KonkArLab/KOSMOS/docs/doc/kosmos/pictures/deployment/filtre_lens.jpg

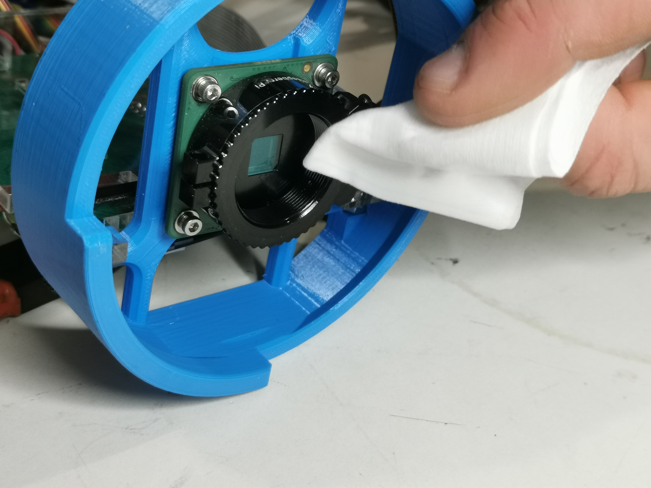
docs/doc/kosmos/pictures/deployment/filtre_lens.jpg
