KonkArLab/KOSMOS/docs/doc/kosmos/pictures/deployment/mire.jpg

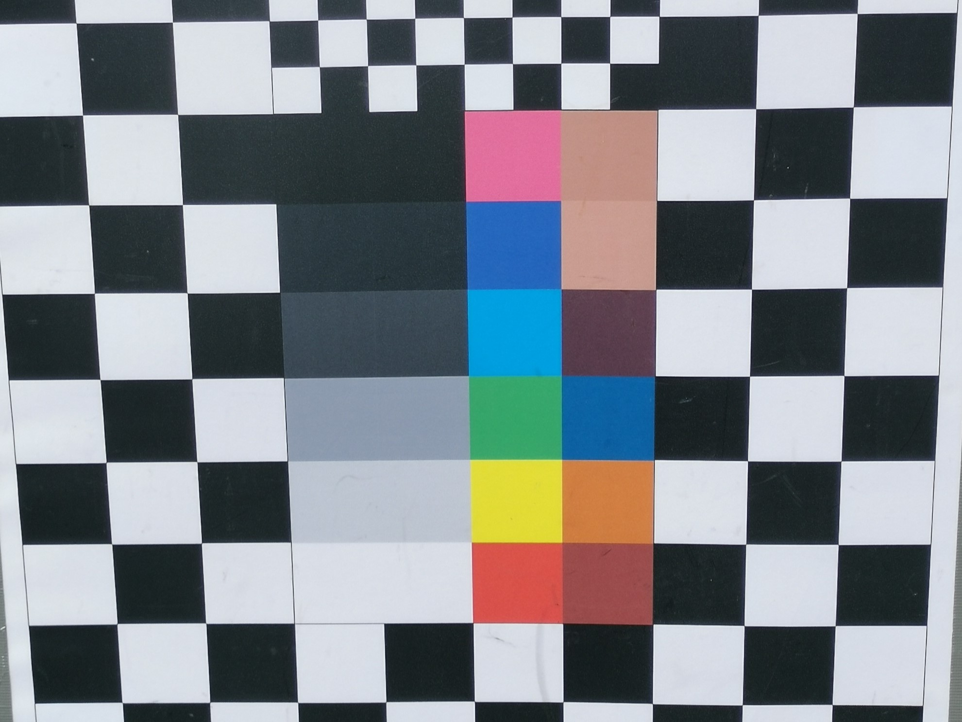
docs/doc/kosmos/pictures/deployment/mire.jpg
