KonkArLab/KOSMOS/docs/doc/kosmos/pictures/deployment/objectif.jpg

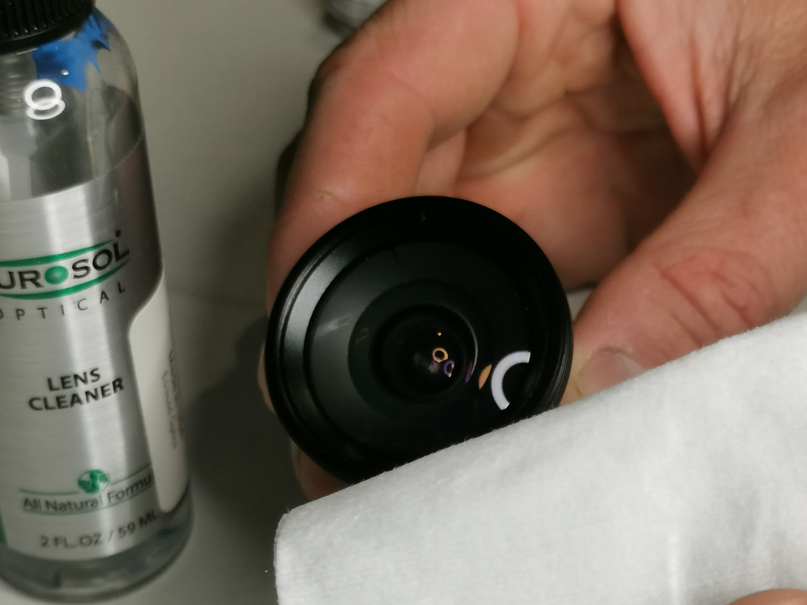
docs/doc/kosmos/pictures/deployment/objectif.jpg
