KonkArLab/KOSMOS/docs/doc/kosmos/pictures/deployment/vis_reglage.jpg

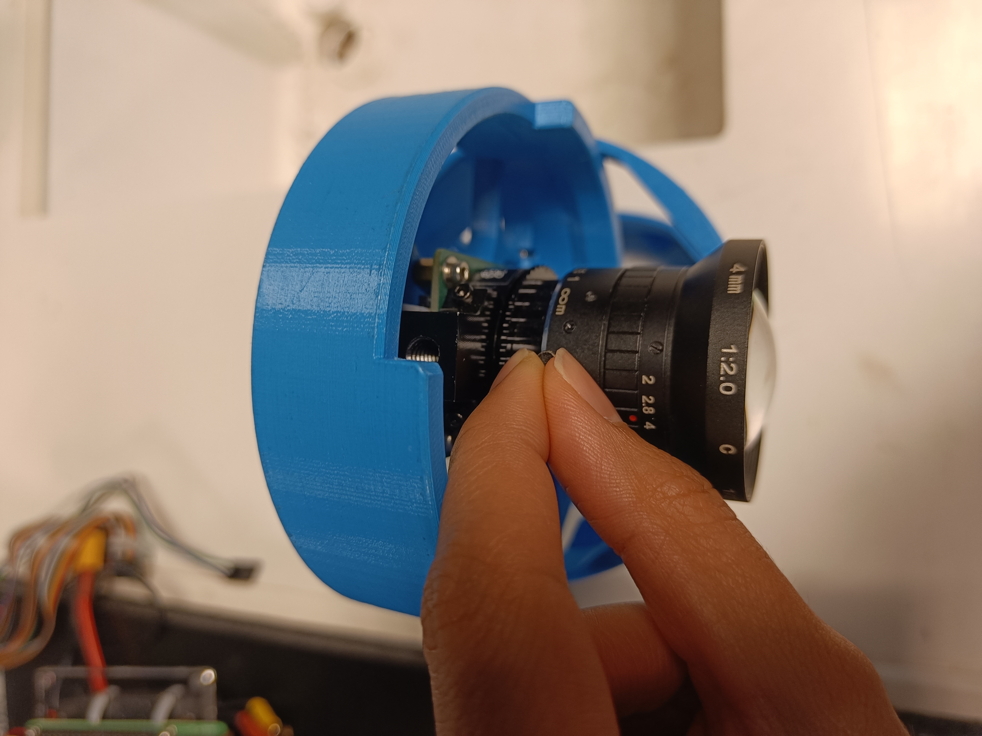
docs/doc/kosmos/pictures/deployment/vis_reglage.jpg
