KonkArLab/KOSMOS/docs/doc/micro_kosmos/pictures/equipments/boitier/clavier_.png

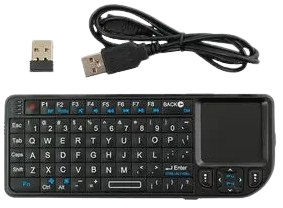
docs/doc/micro_kosmos/pictures/equipments/boitier/clavier_.png
