KonkArLab/KOSMOS/docs/doc/micro_kosmos/pictures/equipments/cable/8pin_cable.png

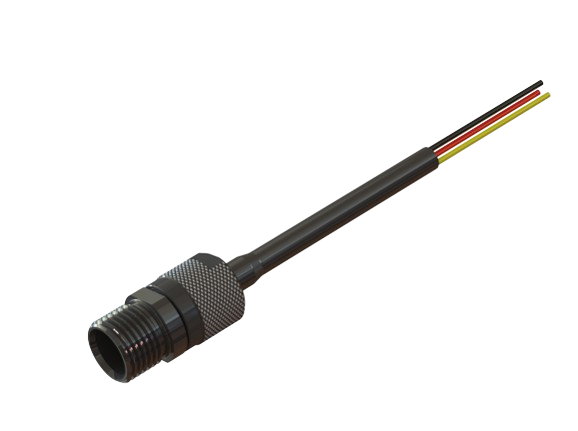
docs/doc/micro_kosmos/pictures/equipments/cable/8pin_cable.png
