KonkArLab/KOSMOS/docs/doc/micro_kosmos/pictures/equipments/caisson_video/ventm10.PNG

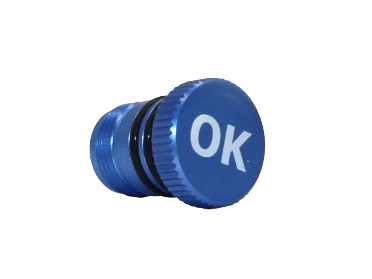
docs/doc/micro_kosmos/pictures/equipments/caisson_video/ventm10.PNG
