KonkArLab/KOSMOS/docs/hardware/kosmos/electronics/electronic.png

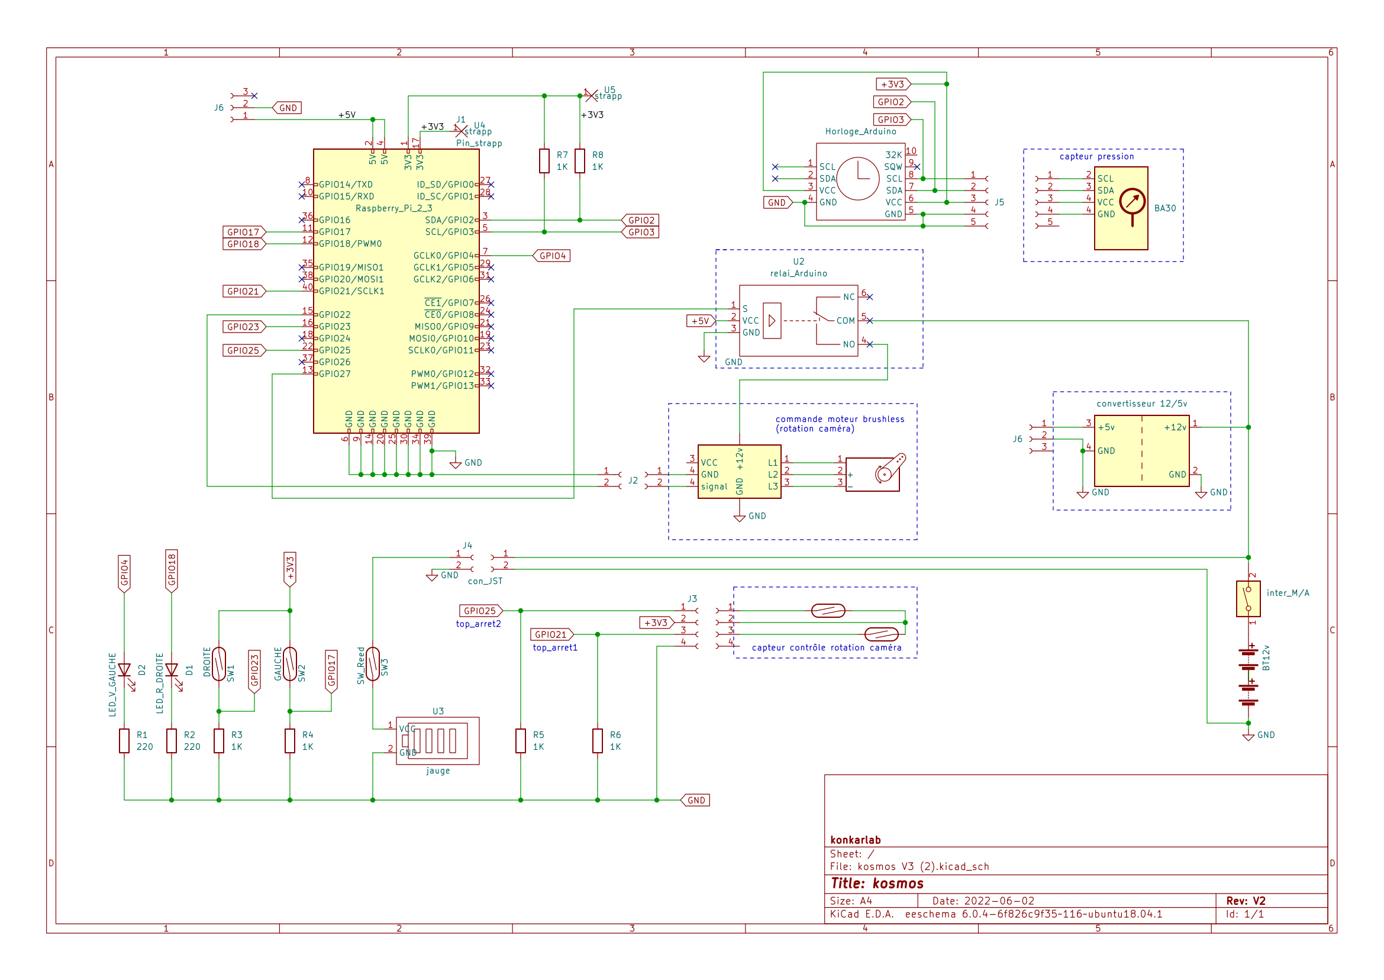
docs/hardware/kosmos/electronics/electronic.png
