KonkArLab/KOSMOS/docs/doc/kosmos/pictures/productions_of_parts/IMG_20230210_140606.jpg

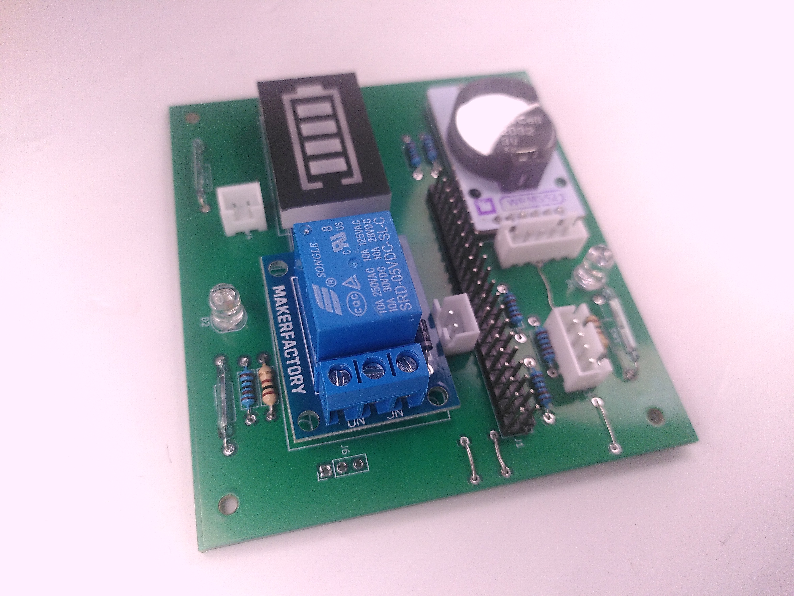
docs/doc/kosmos/pictures/productions_of_parts/IMG_20230210_140606.jpg
