KonkArLab/KOSMOS/docs/doc/kosmos/pictures/productions_of_parts/POP1-1.PNG

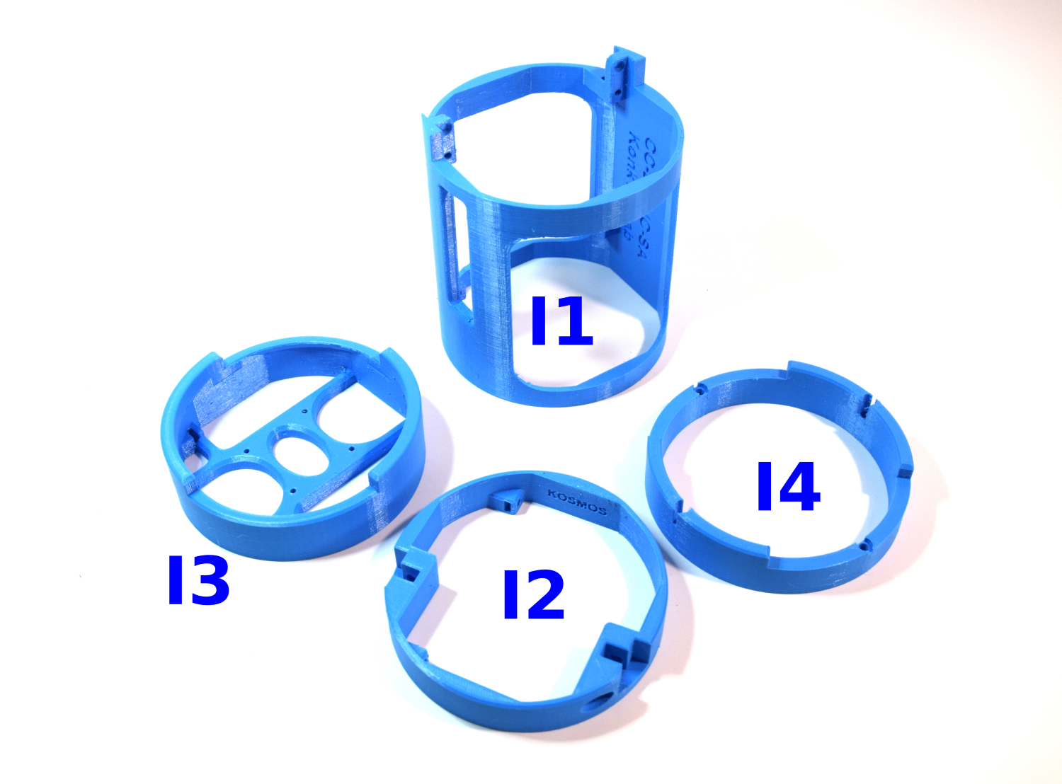
docs/doc/kosmos/pictures/productions_of_parts/POP1-1.PNG
