KonkArLab/KOSMOS/docs/doc/kosmos/pictures/productions_of_parts/POP1-2.PNG

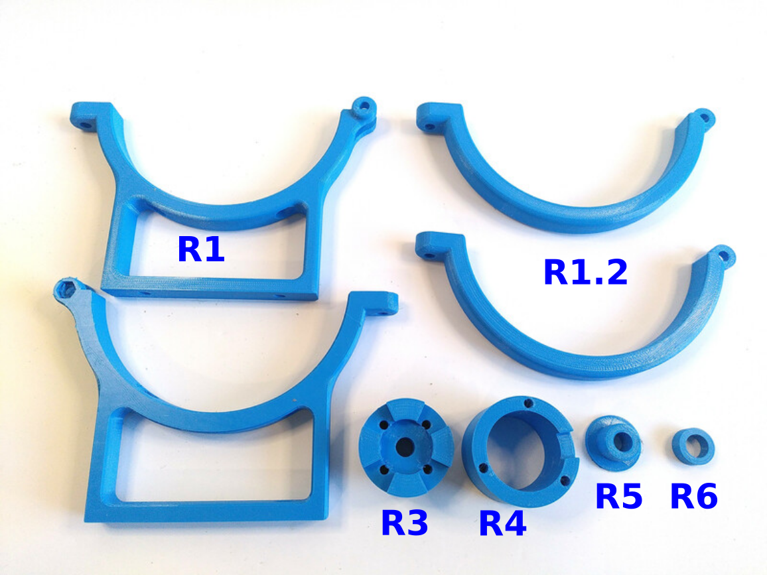
docs/doc/kosmos/pictures/productions_of_parts/POP1-2.PNG
