KonkArLab/KOSMOS/docs/hardware/kosmos/3Dprint_files/R3_KOSMOS_V3-0.stl

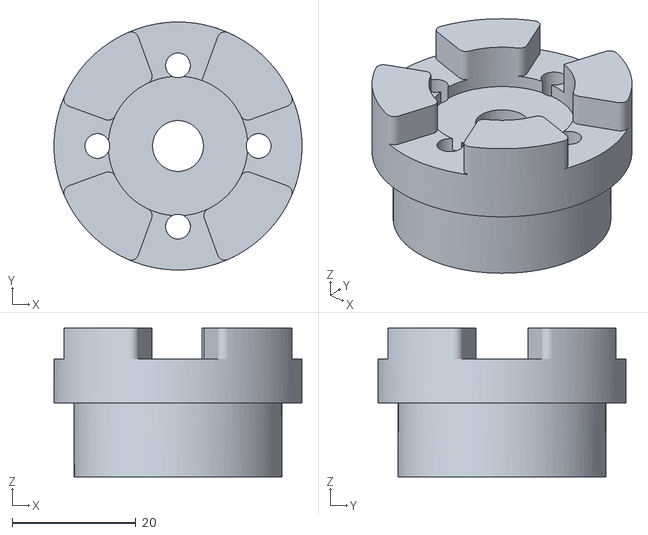
[picture p152: CAD file, 2022-07-12]
docs/hardware/kosmos/3Dprint_files/R3_KOSMOS_V3-0.stl
40.0 x 40.0 x 24.0
