KonkArLab/KOSMOS/docs/hardware/kosmos/3Dprint_files/I2_KOSMOS_V3-0.stl

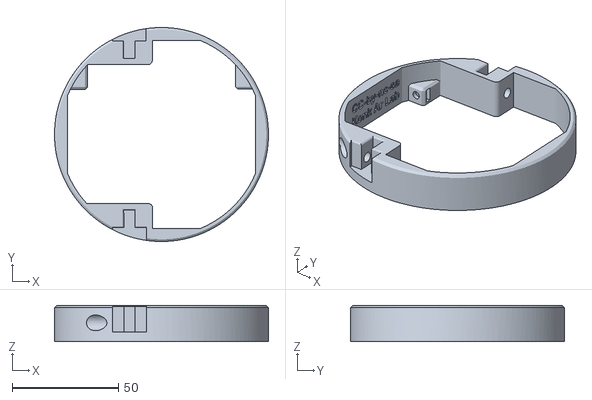
[picture p153: CAD file, 2022-07-12]
docs/hardware/kosmos/3Dprint_files/I2_KOSMOS_V3-0.stl
100.9 x 100.9 x 17.0
