KonkArLab/KOSMOS/docs/hardware/kosmos/3Dprint_files/R6_KOSMOS_V3-0.stl

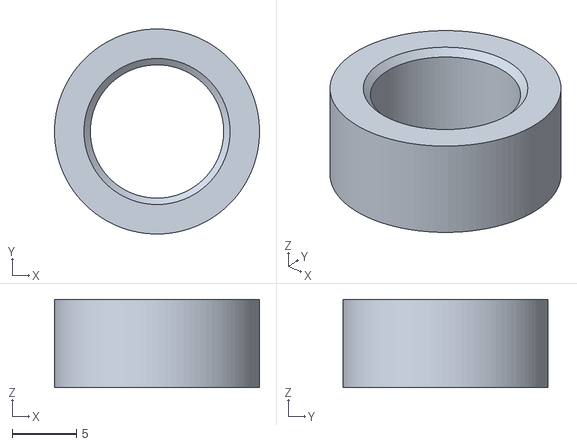
[picture p154: CAD file, 2022-07-12]
docs/hardware/kosmos/3Dprint_files/R6_KOSMOS_V3-0.stl
16.0 x 16.0 x 6.90
