KonkArLab/KOSMOS/docs/hardware/kosmos/3Dprint_files/I4_KOSMOS_V3-0.stl

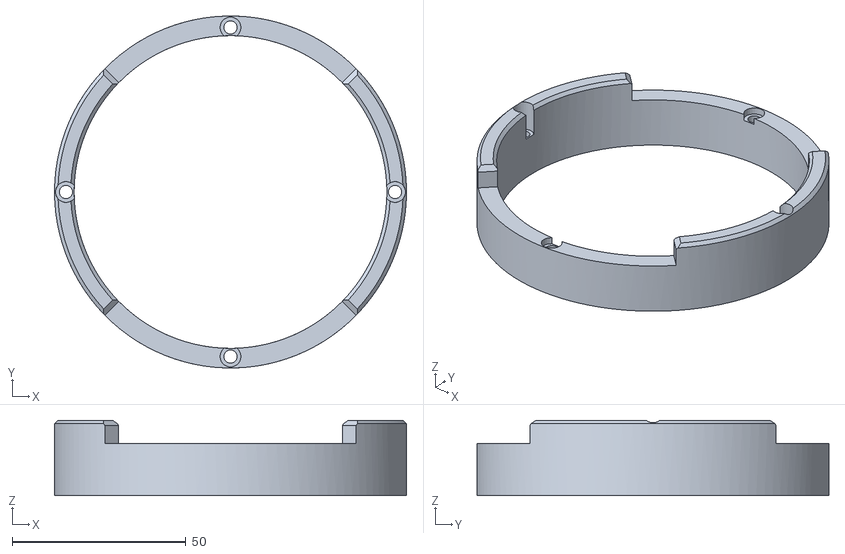
[picture p155: CAD file, 2022-07-12]
docs/hardware/kosmos/3Dprint_files/I4_KOSMOS_V3-0.stl
101.2 x 101.2 x 21.7
