KonkArLab/KOSMOS/docs/hardware/kosmos/3Dprint_files/R5_KOSMOS_V3-0.stl

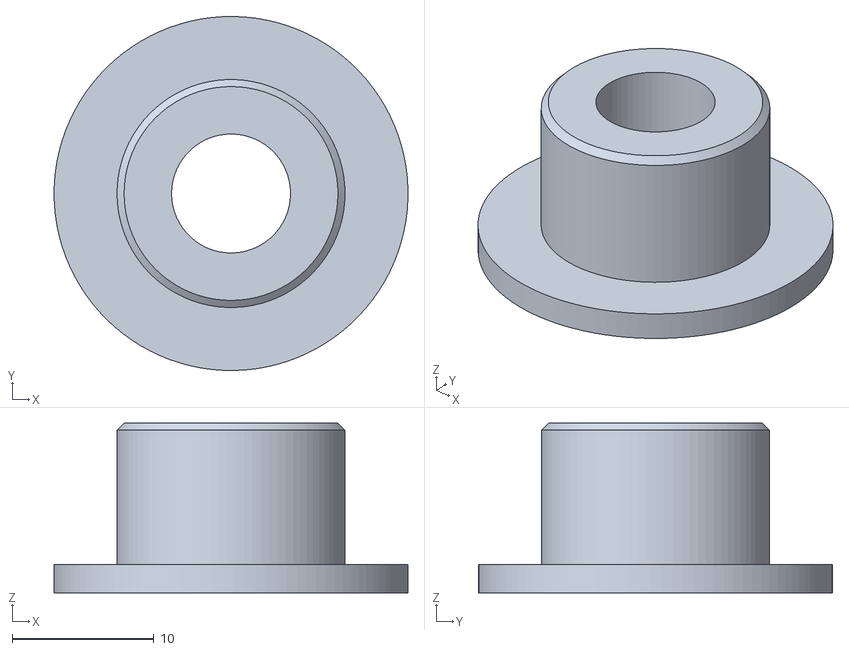
[picture p157: CAD file, 2022-07-12]
docs/hardware/kosmos/3Dprint_files/R5_KOSMOS_V3-0.stl
25.0 x 25.0 x 12.0
