KonkArLab/KOSMOS/docs/hardware/kosmos/3Dprint_files/R4_KOSMOS_V3-0.stl

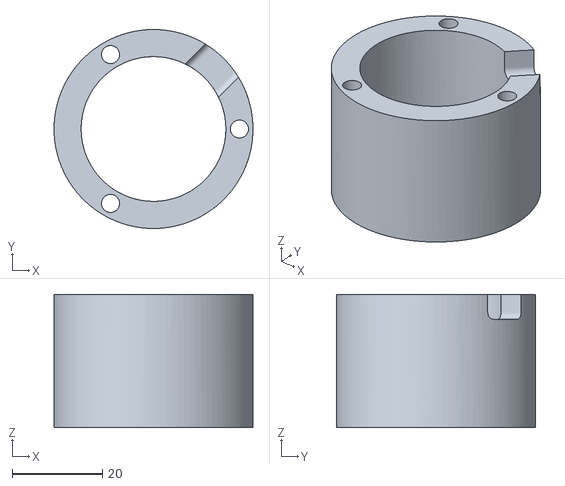
[picture p158: CAD file, 2022-07-12]
docs/hardware/kosmos/3Dprint_files/R4_KOSMOS_V3-0.stl
44.0 x 44.0 x 29.5
