KonkArLab/KOSMOS/docs/hardware/kosmos/3Dprint_files/R1-2_KOSMOS_V3-0.stl

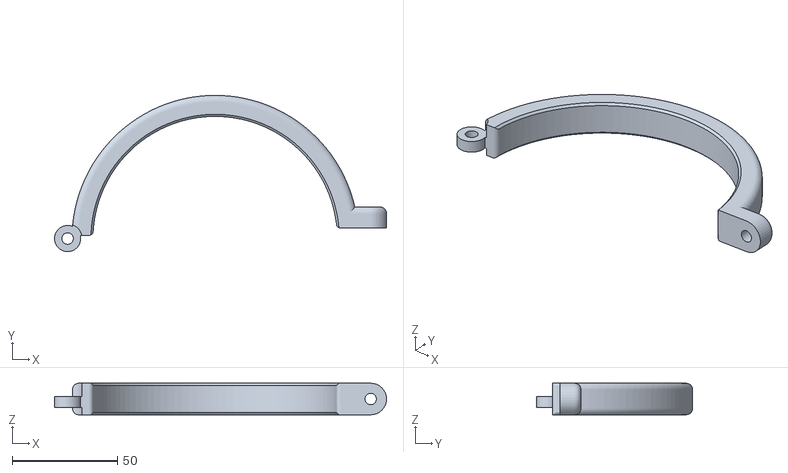
[picture p159: CAD file, 2022-07-12]
docs/hardware/kosmos/3Dprint_files/R1-2_KOSMOS_V3-0.stl
157.6 x 74.2 x 15.0
