KonkArLab/KOSMOS/docs/hardware/kosmos/3Dprint_files/R2_KOSMOS_V3-0.stl

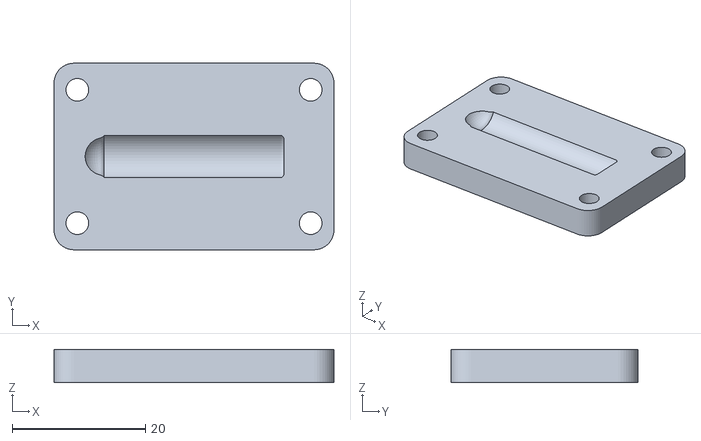
[picture p160: CAD file, 2022-07-12]
docs/hardware/kosmos/3Dprint_files/R2_KOSMOS_V3-0.stl
42.0 x 28.0 x 5.00
