KonkArLab/KOSMOS/docs/doc/kosmos/pictures/assembly_guide/AG1-2.JPG

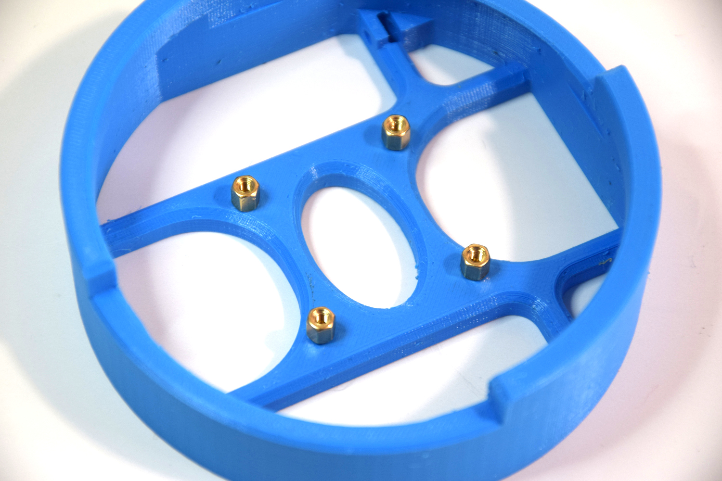
docs/doc/kosmos/pictures/assembly_guide/AG1-2.JPG
