KonkArLab/KOSMOS/docs/doc/kosmos/pictures/assembly_guide/AG1-4.JPG

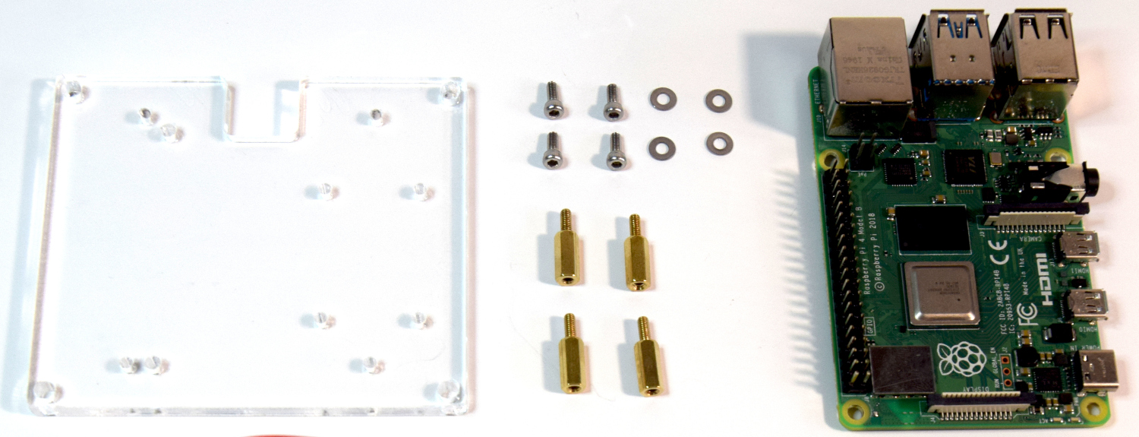
docs/doc/kosmos/pictures/assembly_guide/AG1-4.JPG
