KonkArLab/KOSMOS/docs/doc/kosmos/pictures/assembly_guide/AG1-7.JPG

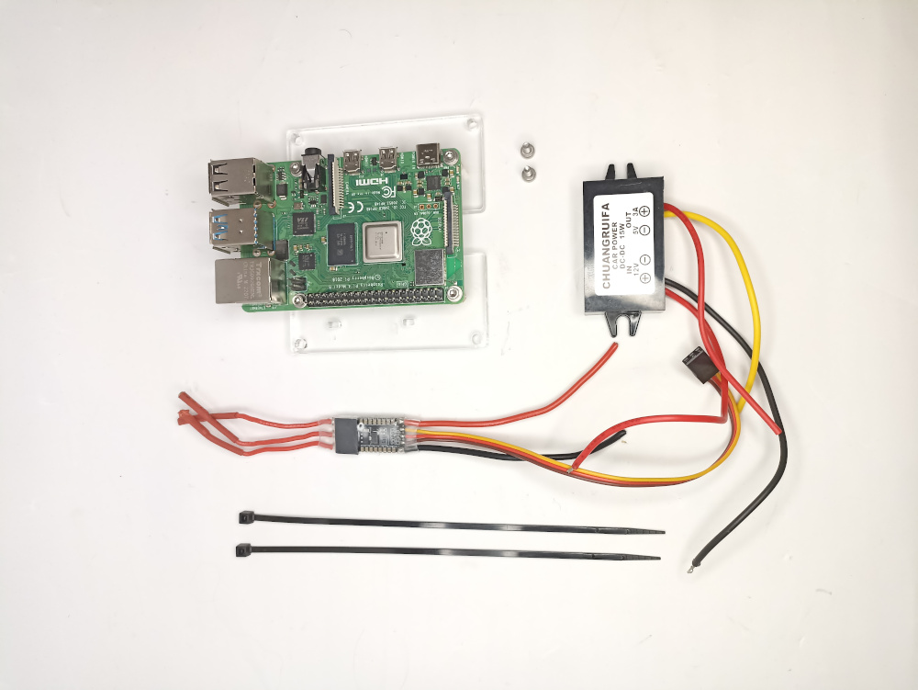
docs/doc/kosmos/pictures/assembly_guide/AG1-7.JPG
