KonkArLab/KOSMOS/docs/doc/kosmos/pictures/assembly_guide/AG1-8.JPG

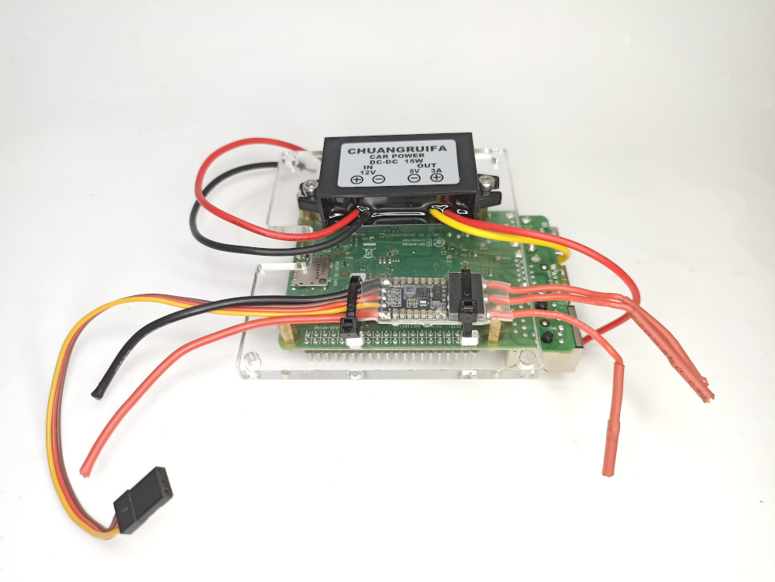
docs/doc/kosmos/pictures/assembly_guide/AG1-8.JPG
