KonkArLab/KOSMOS/docs/doc/kosmos/pictures/assembly_guide/AG1-9.JPG

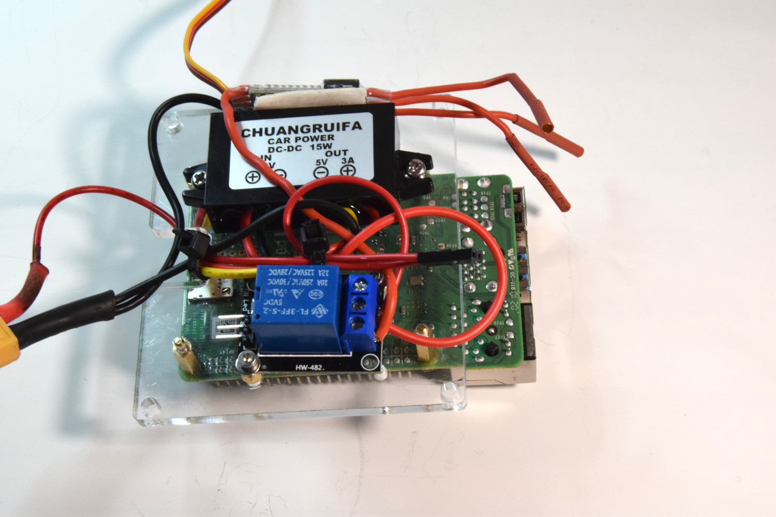
docs/doc/kosmos/pictures/assembly_guide/AG1-9.JPG
