KonkArLab/KOSMOS/docs/doc/kosmos/pictures/assembly_guide/AG1-13.JPG

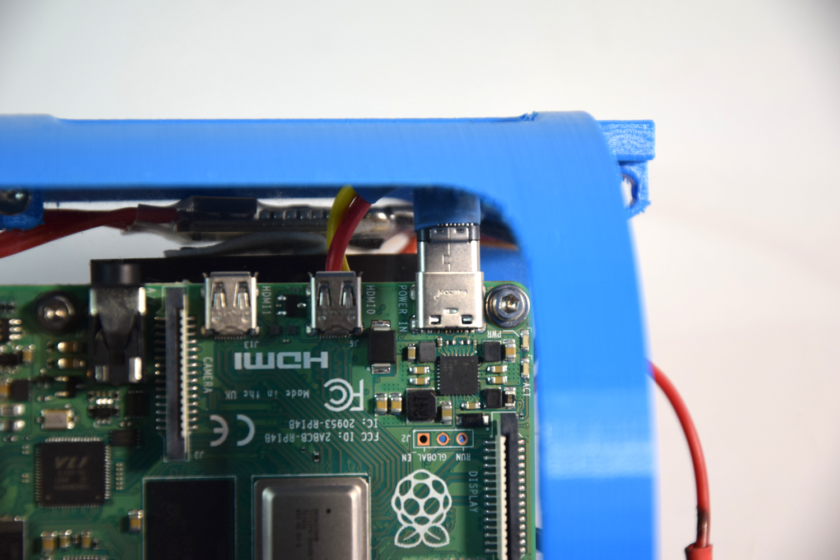
docs/doc/kosmos/pictures/assembly_guide/AG1-13.JPG
