KonkArLab/KOSMOS/docs/doc/kosmos/pictures/assembly_guide/AG3-6.JPG

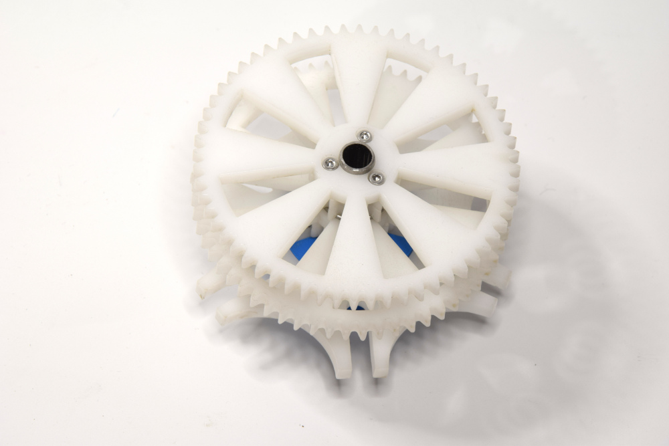
docs/doc/kosmos/pictures/assembly_guide/AG3-6.JPG
