KonkArLab/KOSMOS/docs/doc/kosmos/pictures/assembly_guide/AG3-8.JPG

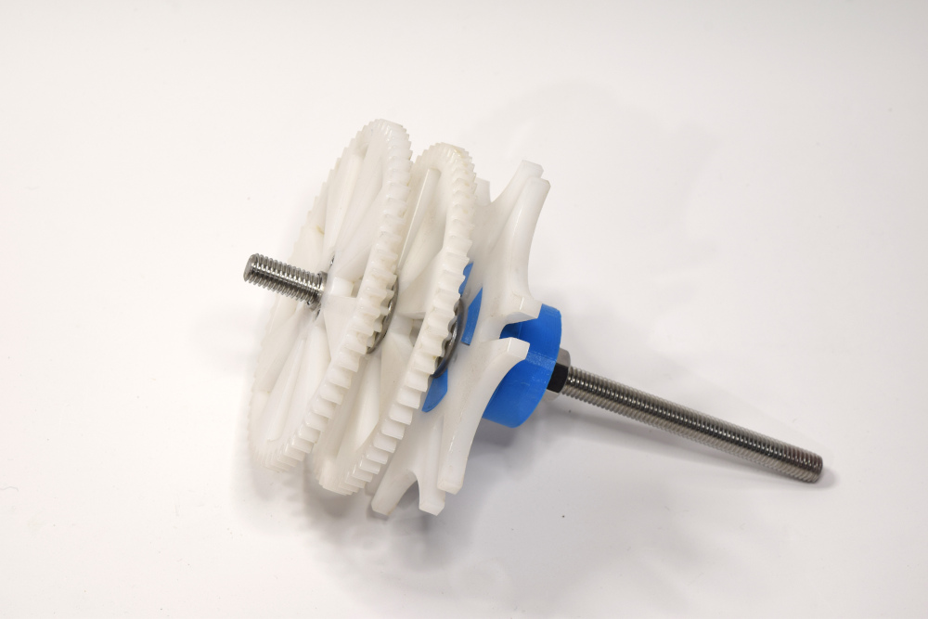
docs/doc/kosmos/pictures/assembly_guide/AG3-8.JPG
