KonkArLab/KOSMOS/docs/doc/kosmos/pictures/install_software/IS1-1.JPG

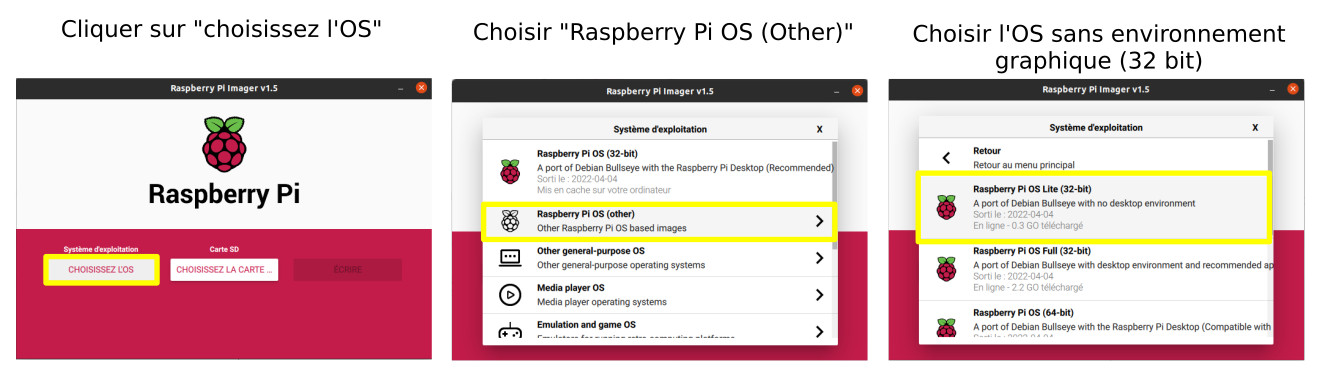
docs/doc/kosmos/pictures/install_software/IS1-1.JPG
