KonkArLab/KOSMOS/docs/doc/kosmos/pictures/install_software/IS1-2.png

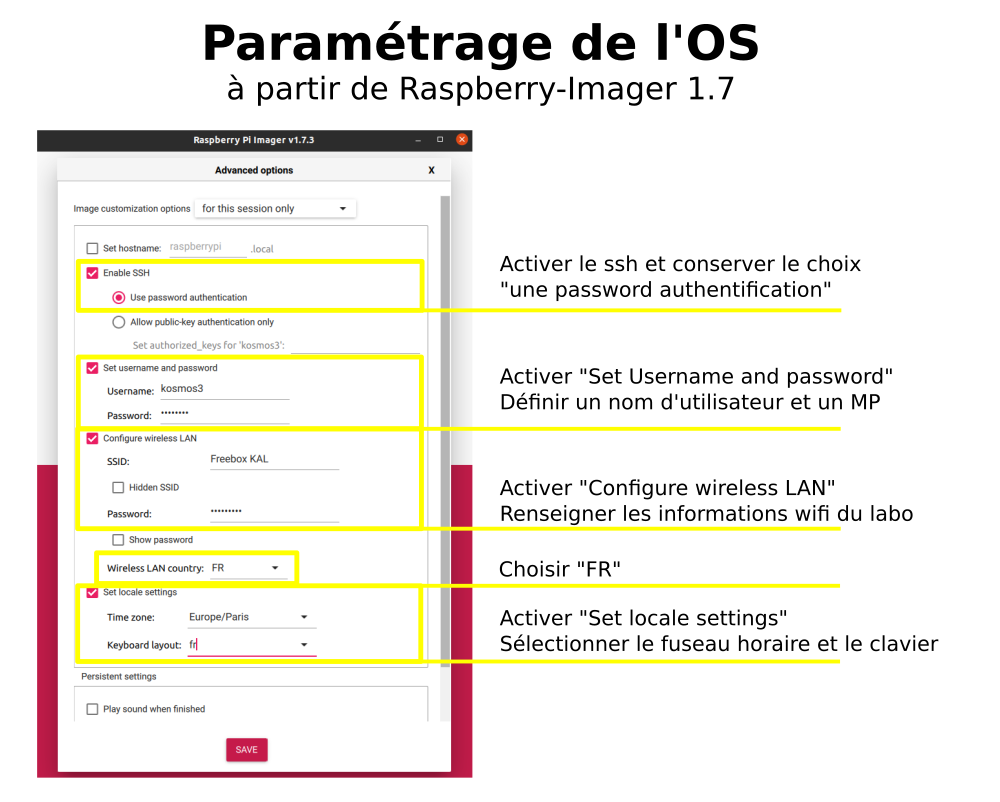
docs/doc/kosmos/pictures/install_software/IS1-2.png
