KonkArLab/KOSMOS/docs/doc/kosmos/pictures/install_software/IS1-3.JPG

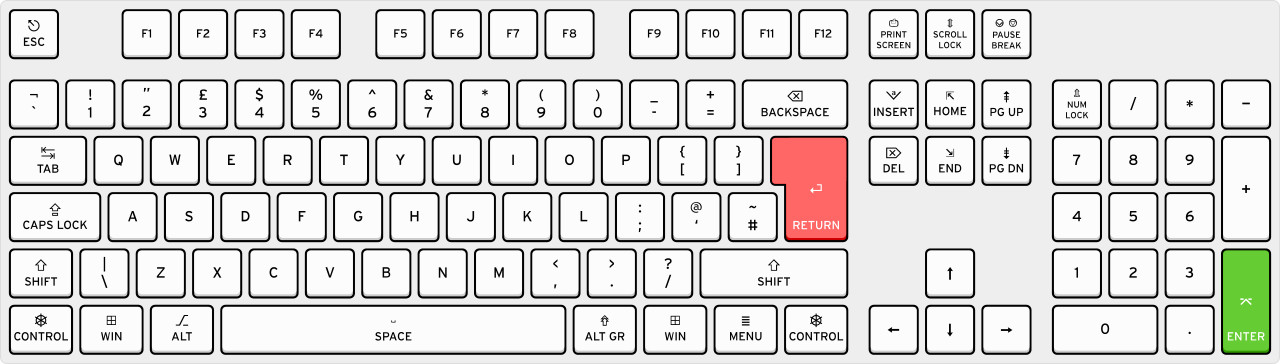
docs/doc/kosmos/pictures/install_software/IS1-3.JPG
