KonkArLab/KOSMOS/docs/doc/micro_kosmos/pictures/assembly_guide/boitier/ajout_connecteur.jpg

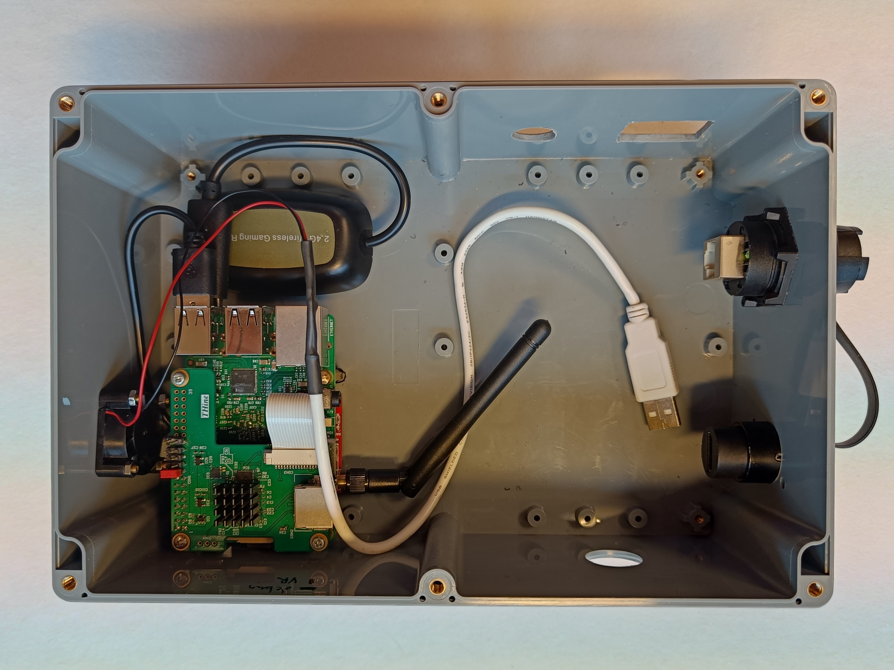
docs/doc/micro_kosmos/pictures/assembly_guide/boitier/ajout_connecteur.jpg
