KonkArLab/KOSMOS/docs/doc/micro_kosmos/pictures/assembly_guide/boitier/gps.jpg

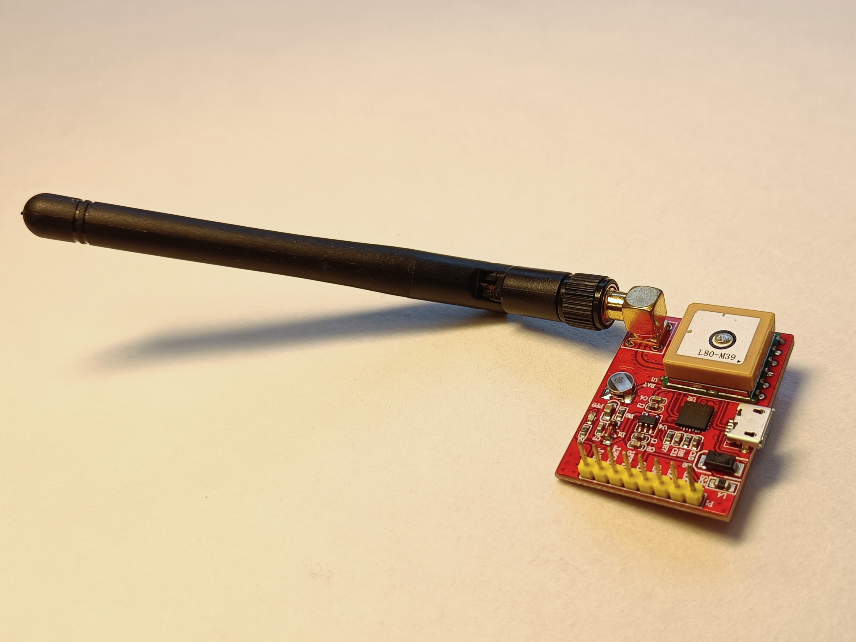
docs/doc/micro_kosmos/pictures/assembly_guide/boitier/gps.jpg
