KonkArLab/KOSMOS/docs/doc/micro_kosmos/pictures/assembly_guide/boitier/velcro_trou.jpg

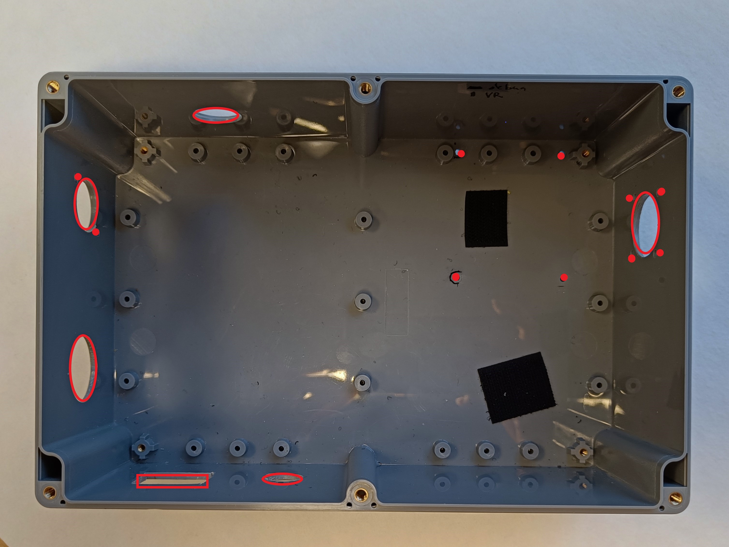
docs/doc/micro_kosmos/pictures/assembly_guide/boitier/velcro_trou.jpg
